hwreverse/PokeConSerial/PC1600SIO/PC1600SIO.jpg

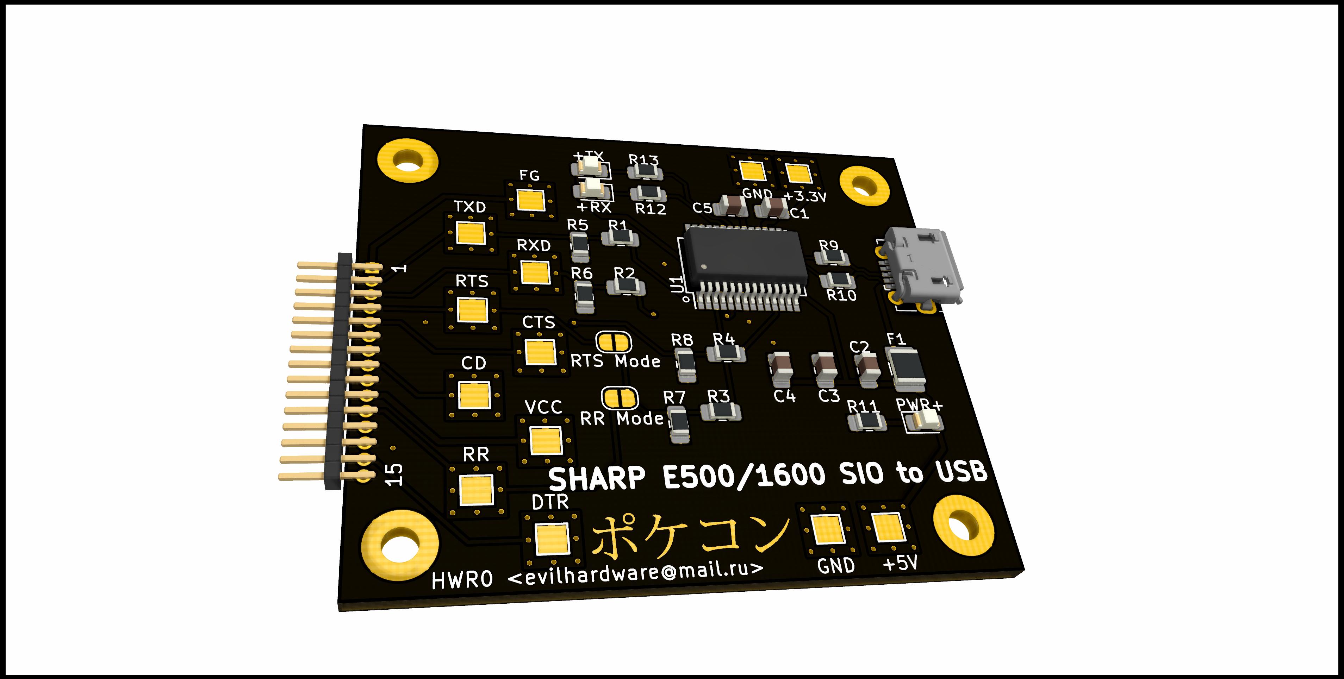
PC1600SIO/PC1600SIO.jpg
