hwreverse/PokeConSerial/PC1600SIO/pokekon.png

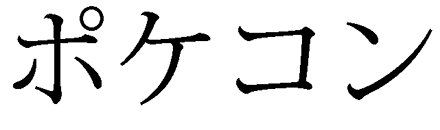
PC1600SIO/pokekon.png
